RetroNynjah/Switchless-Multi-ROM-for-27128-27256/applications/Switchless multi-kernal for C64 shortboard and C128/mini-kernal/C128 v1.5/constants.asm

D6510 = $00
R6510 = $01
BANK = $02

PALNTS = $0a03
VICREG = $d000
MMU_LO = $d500
MMUMCR = $d505
VDCADR = $d600
VDCDAT = $d601

PORTA = $dc00
PORTB = $dc01
EXTKB = $d02f
DDRA = $dc02
DDRB = $dc03
MMUCR = $ff00


; VDC colors
VDC_BLACK = 0
VDC_LIGHTBLACK = 1
VDC_DARKBLUE = 2
VDC_LIGHTBLUE = 3
VDC_DARKGREEN = 4
VDC_LIGHTGREEN = 5
VDC_DARKCYAN = 6
VDC_LIGHTCYAN = 7
VDC_DARKRED = 8
VDC_LIGHTRED = 9
VDC_DARKPURPLE = 10
VDC_LIGHTPURPLE = 11
VDC_DARKYELLOW = 12
VDC_LIGHTYELLOW = 13
VDC_DARKWHITE = 14
VDC_WHITE = 15

; VDC attributes
VDC_BLINK = 16
VDC_UNDERLINE = 32
VDC_REVERSE = 64
VDC_ALTERNATE = 128
